Brawn1/ESP-Air-Quality-Logger/kicad/schaltplan/schaltplan.kicad_sch

## KiCad design kicad/schaltplan/schaltplan.kicad_sch (2026-07-07)

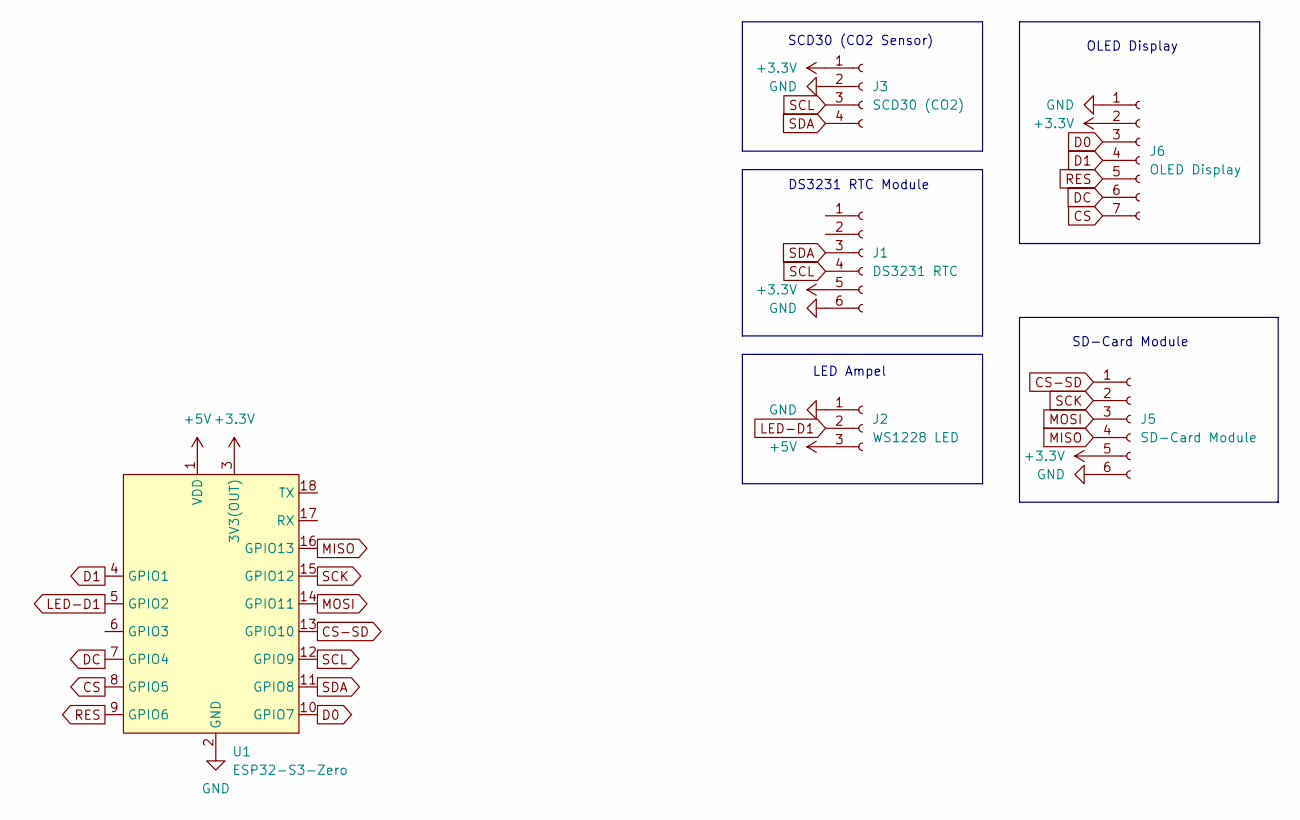
[picture p1: schematic schaltplan.kicad_sch]

Parts:
J1: DS3231 RTC
J2: WS1228 LED
J3: SCD30 (CO2)
J5: SD-Card Module
J6: OLED Display
U1: ESP32-S3-Zero

Connections:
+3.3V: J1.5, J3.1, J5.5, J6.2, U1.3 (3V3(OUT))
+5V: J2.3, U1.1 (VDD)
CS: J6.7, U1.8 (GPIO5)
CS-SD: J5.1, U1.13 (GPIO10)
D0: J6.3, U1.10 (GPIO7)
D1: J6.4, U1.4 (GPIO1)
DC: J6.6, U1.7 (GPIO4)
GND: J1.6, J2.1, J3.2, J5.6, J6.1, U1.2 (GND)
LED-D1: J2.2, U1.5 (GPIO2)
MISO: J5.4, U1.16 (GPIO13)
MOSI: J5.3, U1.14 (GPIO11)
RES: J6.5, U1.9 (GPIO6)
SCK: J5.2, U1.15 (GPIO12)
SCL: J1.4, J3.3, U1.12 (GPIO9)
SDA: J1.3, J3.4, U1.11 (GPIO8)

Notes on the sheet:
OLED Display
SD-Card Module
LED Ampel
DS3231 RTC Module
SCD30 (CO2 Sensor)
