Brawn1/ESP-Air-Quality-Logger/code/Led.h

// ============================================================================
//  Led.h  -  Onboard-WS2812-RGB-LED als CO2-Ampel (eigener Pin, kein Mutex noetig)
// ============================================================================
#pragma once
#include "config.h"

void ledBegin();
void ledStartupTest();  // Boot-Selbsttest: Lauflicht + alle LEDs R/G/B (Verdrahtung pruefen)
void ledSetCo2(float co2, bool valid);
void ledConfirm();      // kurzes gruenes Blinken (Bestaetigung, z.B. Kalibrierung)
